splitkb/aurora/Aurora Lily58/Aurora Lily58 Top Plate - 0.1mm Kerf.dxf

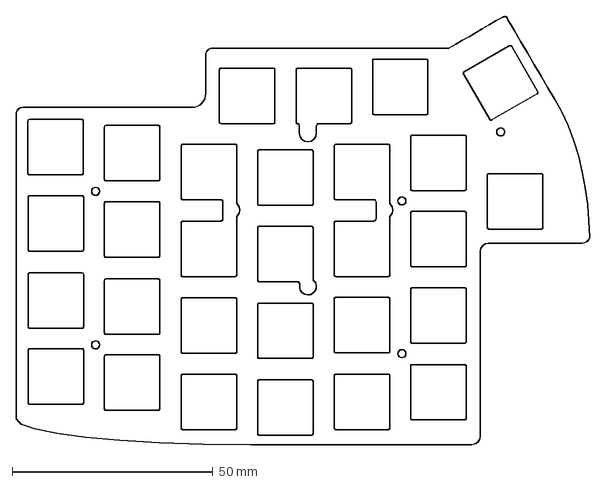
[picture p13: CAD file, 2023-04-05]
Aurora Lily58/Aurora Lily58 Top Plate - 0.1mm Kerf.dxf
142.7 x 106.5 mm
