splitkb/aurora/Aurora Corne/Aurora Corne Bottom Plate - No kerf.dxf

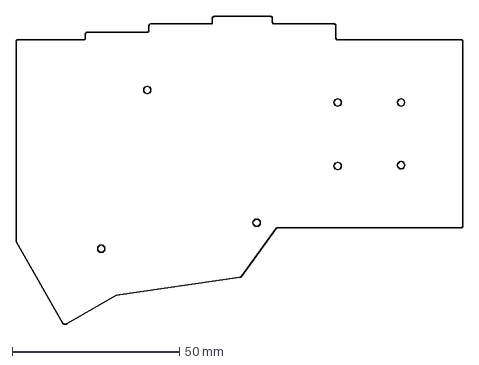
[picture p16: CAD file, 2024-12-12]
Aurora Corne/Aurora Corne Bottom Plate - No kerf.dxf
133.8 x 92.2 mm
