splitkb/aurora/Aurora Helix/Aurora Helix OLED Cover - 0.1mm Kerf.dxf

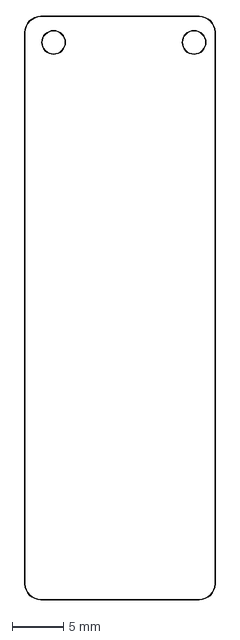
[picture p17: CAD file, 2023-07-05]
Aurora Helix/Aurora Helix OLED Cover - 0.1mm Kerf.dxf
18.6 x 57.1 mm
