splitkb/aurora/Aurora Sofle v2/Aurora Sofle v2 OLED Cover - 0.1mm Kerf.dxf

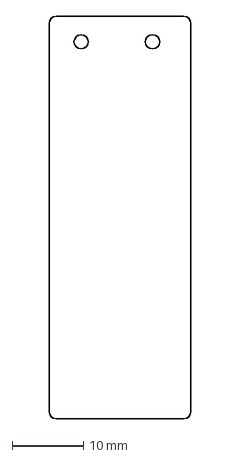
[picture p19: CAD file, 2023-06-28]
Aurora Sofle v2/Aurora Sofle v2 OLED Cover - 0.1mm Kerf.dxf
19.9 x 56.5 mm
