splitkb/aurora/Aurora Sweep/Aurora Sweep Bottom Plate - Puck - 0.1mm Kerf.dxf

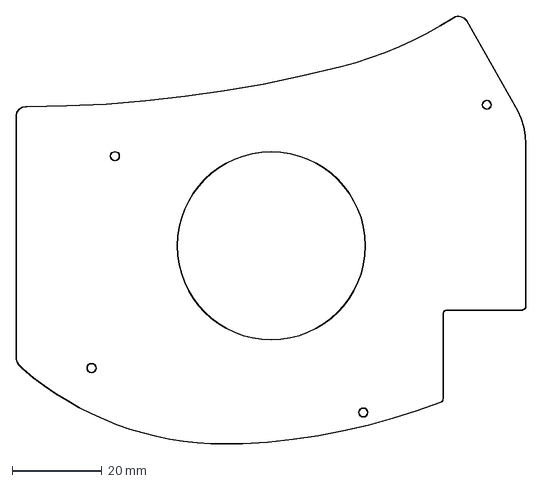
[picture p20: CAD file, 2023-04-05]
Aurora Sweep/Aurora Sweep Bottom Plate - Puck - 0.1mm Kerf.dxf
113.7 x 95.4 mm
