splitkb/aurora/Aurora Corne/Aurora Corne OLED Cover - No Kerf.dxf

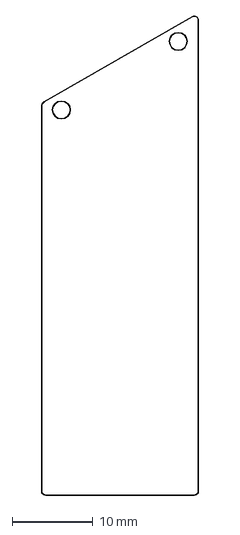
[picture p21: CAD file, 2024-01-22]
Aurora Corne/Aurora Corne OLED Cover - No Kerf.dxf
19.5 x 59.4 mm
