splitkb/aurora/Aurora Sweep/Aurora Sweep Bottom Plate - No Kerf.dxf

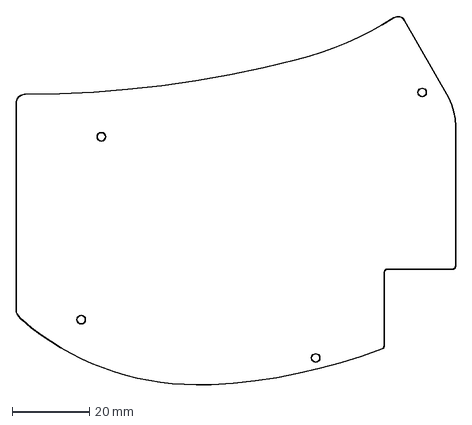
[picture p25: CAD file, 2023-04-05]
Aurora Sweep/Aurora Sweep Bottom Plate - No Kerf.dxf
113.5 x 95.2 mm
