splitkb/aurora/Aurora Helix/Aurora Helix Bottom Plate - Puck - No Kerf.dxf

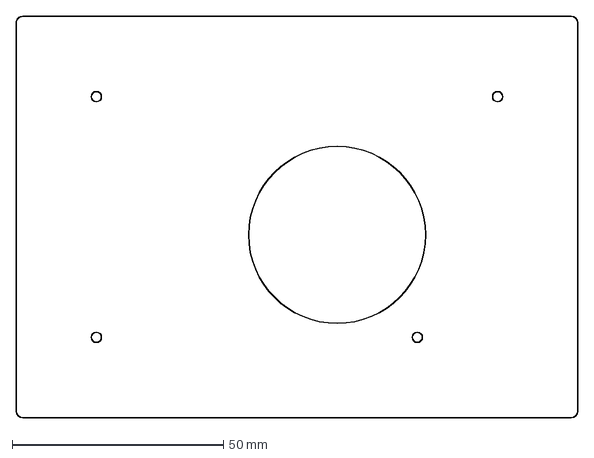
[picture p26: CAD file, 2023-07-05]
Aurora Helix/Aurora Helix Bottom Plate - Puck - No Kerf.dxf
133.0 x 95.0 mm
