splitkb/aurora/Aurora Lily58/Aurora Lily58 Bottom Plate - 0.1mm Kerf.dxf

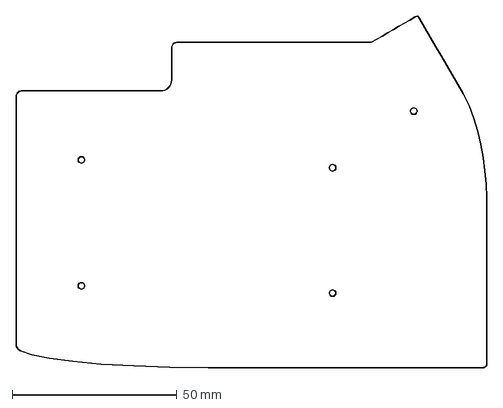
[picture p27: CAD file, 2023-04-05]
Aurora Lily58/Aurora Lily58 Bottom Plate - 0.1mm Kerf.dxf
142.7 x 106.5 mm
