splitkb/aurora/Aurora Sweep/Aurora Sweep Top Plate - Encoder - No Kerf.dxf

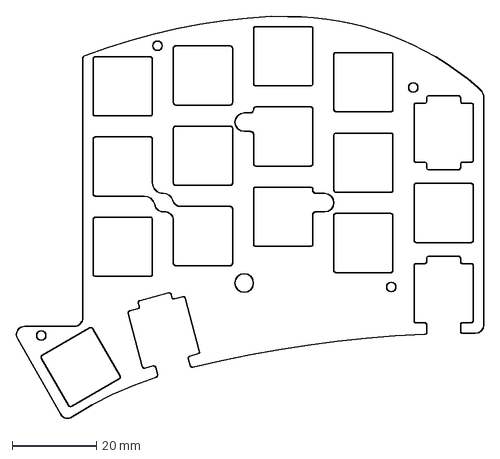
[picture p29: CAD file, 2023-04-05]
Aurora Sweep/Aurora Sweep Top Plate - Encoder - No Kerf.dxf
110.8 x 95.2 mm
