splitkb/aurora/Aurora Corne/Aurora Corne Top Plate - 0.1mm kerf.dxf

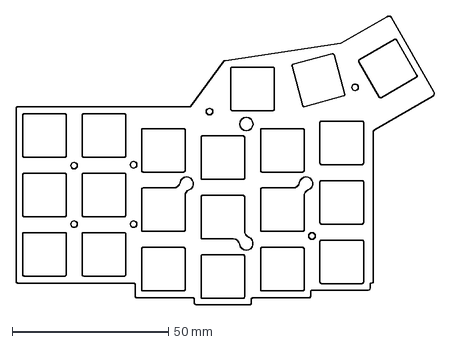
[picture p30: CAD file, 2023-04-05]
Aurora Corne/Aurora Corne Top Plate - 0.1mm kerf.dxf
133.8 x 92.3 mm
