splitkb/aurora/Aurora Helix/Aurora Helix Top Plate - No Kerf.dxf

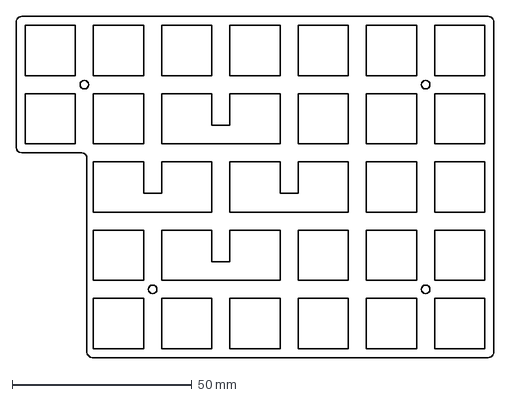
[picture p31: CAD file, 2023-07-05]
Aurora Helix/Aurora Helix Top Plate - No Kerf.dxf
133.0 x 95.0 mm
