splitkb/aurora/Aurora Lily58/Aurora Lily58 OLED Cover - 0.1mm Kerf.dxf

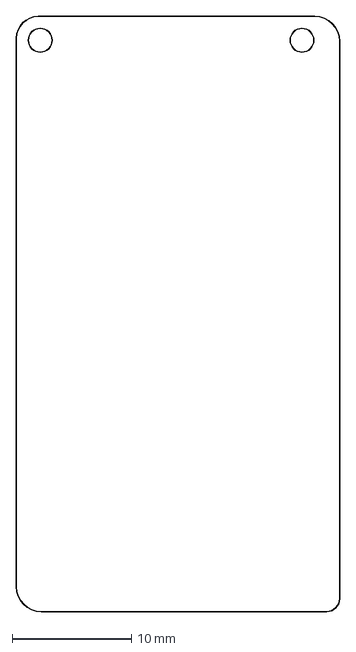
[picture p32: CAD file, 2023-04-05]
Aurora Lily58/Aurora Lily58 OLED Cover - 0.1mm Kerf.dxf
27.2 x 50.0 mm
