splitkb/aurora/Aurora Sofle v2/Aurora Sofle v2 Bottom Plate - Puck - 0.1mm Kerf.dxf

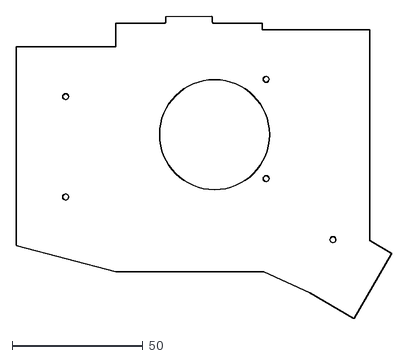
[picture p33: CAD file, 2023-04-05]
Aurora Sofle v2/Aurora Sofle v2 Bottom Plate - Puck - 0.1mm Kerf.dxf
143.3 x 115.3
