splitkb/aurora/Aurora Corne/Aurora Corne Bottom Plate - Puck - No kerf.dxf

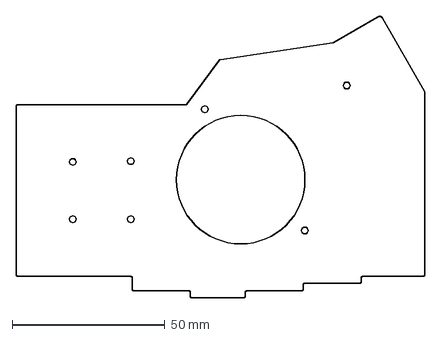
[picture p35: CAD file, 2023-04-05]
Aurora Corne/Aurora Corne Bottom Plate - Puck - No kerf.dxf
133.8 x 92.2 mm
