splitkb/aurora/Aurora Sweep/Aurora Sweep Bottom Plate - Puck - No Kerf.dxf

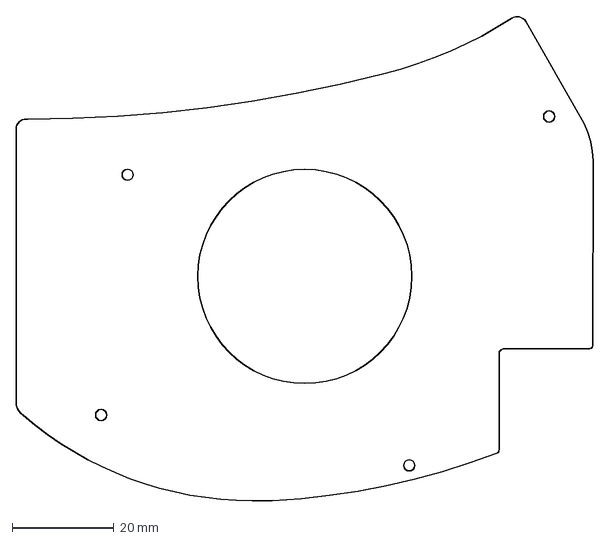
[picture p39: CAD file, 2023-04-05]
Aurora Sweep/Aurora Sweep Bottom Plate - Puck - No Kerf.dxf
113.5 x 95.2 mm
