splitkb/aurora/Aurora Corne/Aurora Corne Top Plate - No Kerf.dxf

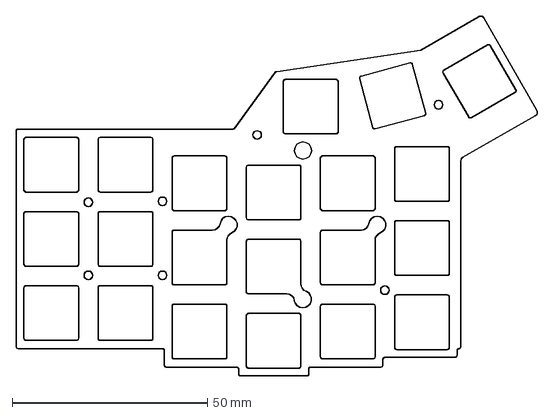
[picture p40: CAD file, 2023-04-05]
Aurora Corne/Aurora Corne Top Plate - No Kerf.dxf
133.7 x 92.2 mm
