splitkb/aurora/Aurora Helix/Aurora Helix Top Plate - 0.1mm Kerf.dxf

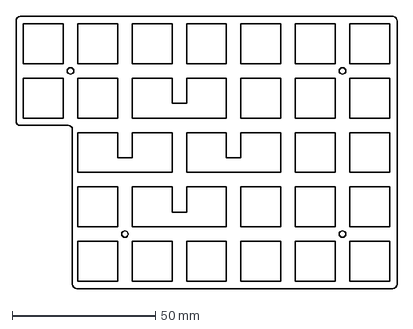
[picture p41: CAD file, 2023-07-05]
Aurora Helix/Aurora Helix Top Plate - 0.1mm Kerf.dxf
133.1 x 95.1 mm
