splitkb/aurora/Aurora Lily58/Aurora Lily58 Bottom Plate - Puck - No Kerf.dxf

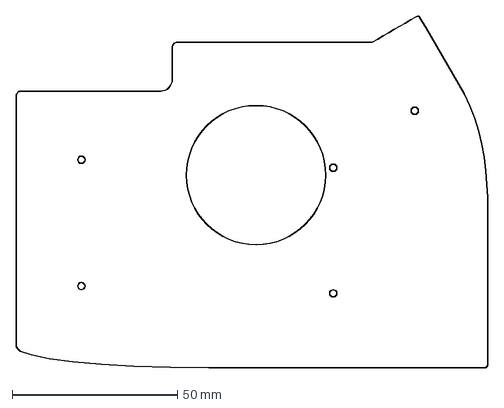
[picture p42: CAD file, 2023-04-05]
Aurora Lily58/Aurora Lily58 Bottom Plate - Puck - No Kerf.dxf
142.5 x 106.3 mm
