splitkb/aurora/Aurora Sweep/Aurora Sweep Top Plate - 0.1mm Kerf.dxf

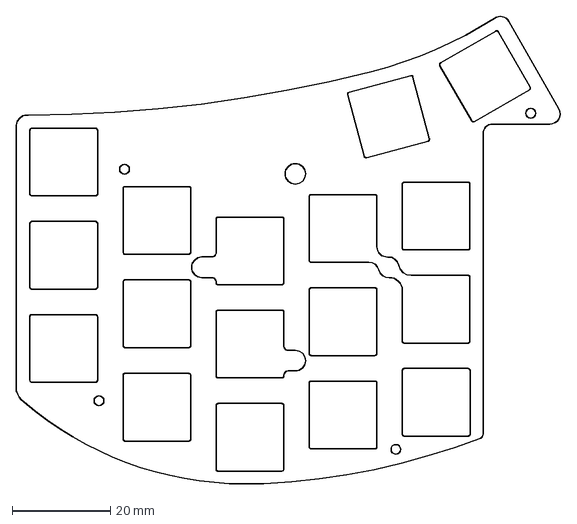
[picture p44: CAD file, 2023-04-05]
Aurora Sweep/Aurora Sweep Top Plate - 0.1mm Kerf.dxf
111.0 x 95.4 mm
