splitkb/aurora/Aurora Corne/Aurora Corne Bottom Plate - Puck - 0.1mm Kerf.dxf

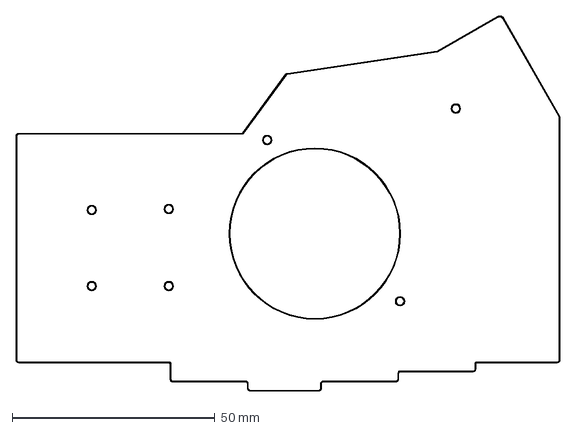
[picture p45: CAD file, 2023-04-05]
Aurora Corne/Aurora Corne Bottom Plate - Puck - 0.1mm Kerf.dxf
134.0 x 92.4 mm
