splitkb/aurora/Aurora Lily58/Aurora Lily58 Top Plate - No Kerf.dxf

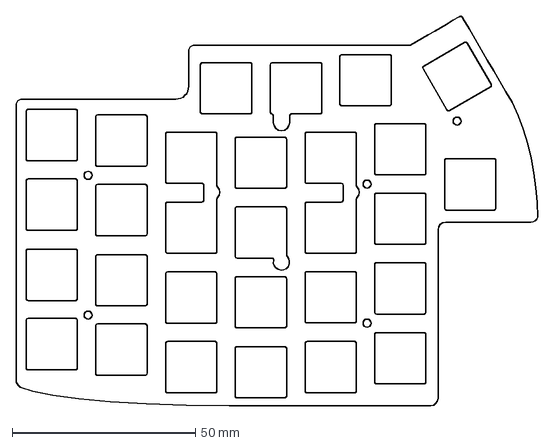
[picture p47: CAD file, 2023-04-05]
Aurora Lily58/Aurora Lily58 Top Plate - No Kerf.dxf
142.5 x 106.3 mm
