splitkb/aurora/Aurora Sweep/Aurora Sweep Top Plate - No Kerf.dxf

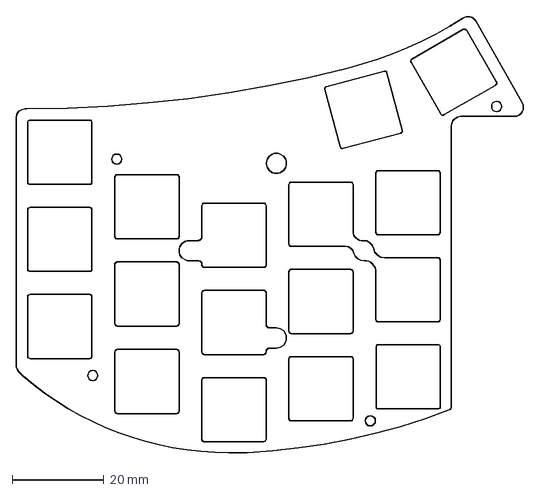
[picture p49: CAD file, 2023-04-05]
Aurora Sweep/Aurora Sweep Top Plate - No Kerf.dxf
110.8 x 95.2 mm
