splitkb/aurora/Aurora Lily58/Aurora Lily58 OLED Cover - No Kerf.dxf

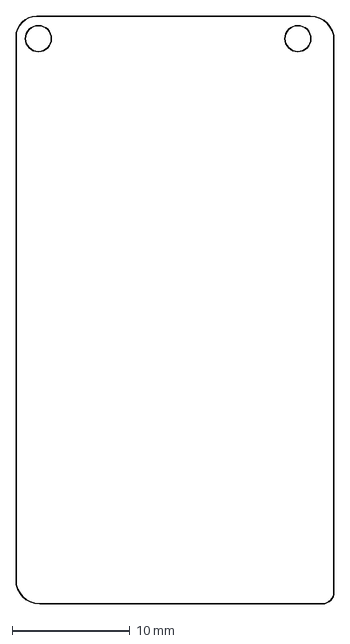
[picture p50: CAD file, 2023-04-05]
Aurora Lily58/Aurora Lily58 OLED Cover - No Kerf.dxf
27.0 x 49.8 mm
