splitkb/aurora/Aurora Sofle v2/Aurora Sofle v2 Top Plate - No Kerf.dxf

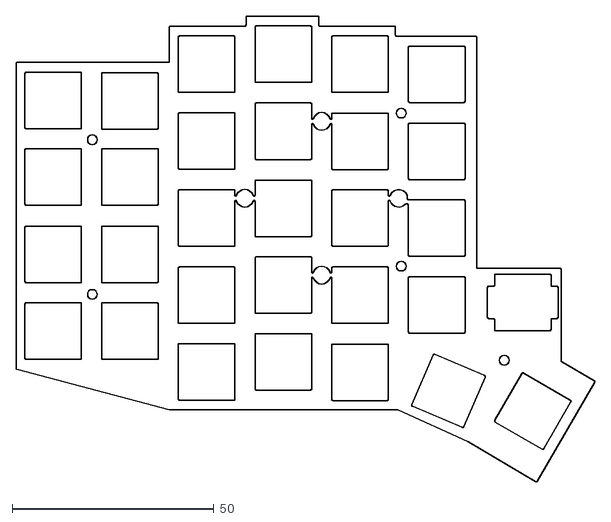
[picture p51: CAD file, 2023-04-05]
Aurora Sofle v2/Aurora Sofle v2 Top Plate - No Kerf.dxf
143.4 x 115.4
