splitkb/aurora/Aurora Sofle v2/Aurora Sofle v2 Top Plate - No Puck - No Kerf.dxf

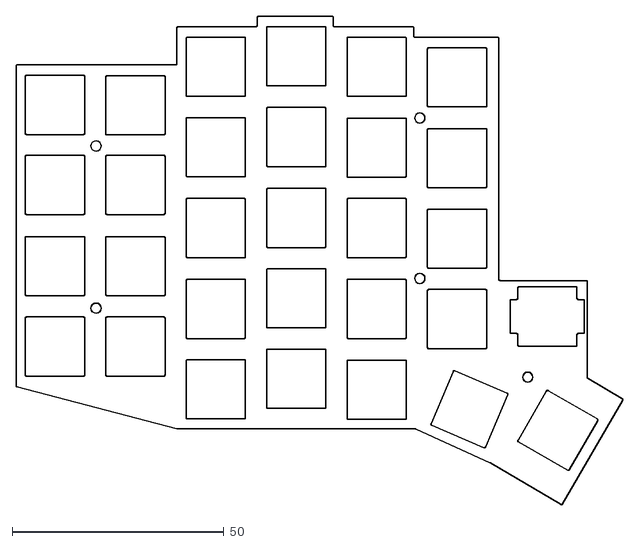
[picture p52: CAD file, 2023-04-05]
Aurora Sofle v2/Aurora Sofle v2 Top Plate - No Puck - No Kerf.dxf
143.4 x 115.4
